SA6HBR/F800_Arduino_ctcss_dtmf/KiCad/F800_arduino_v1.kicad_sch

## KiCad design KiCad/F800_arduino_v1.kicad_sch (2022-08-06)

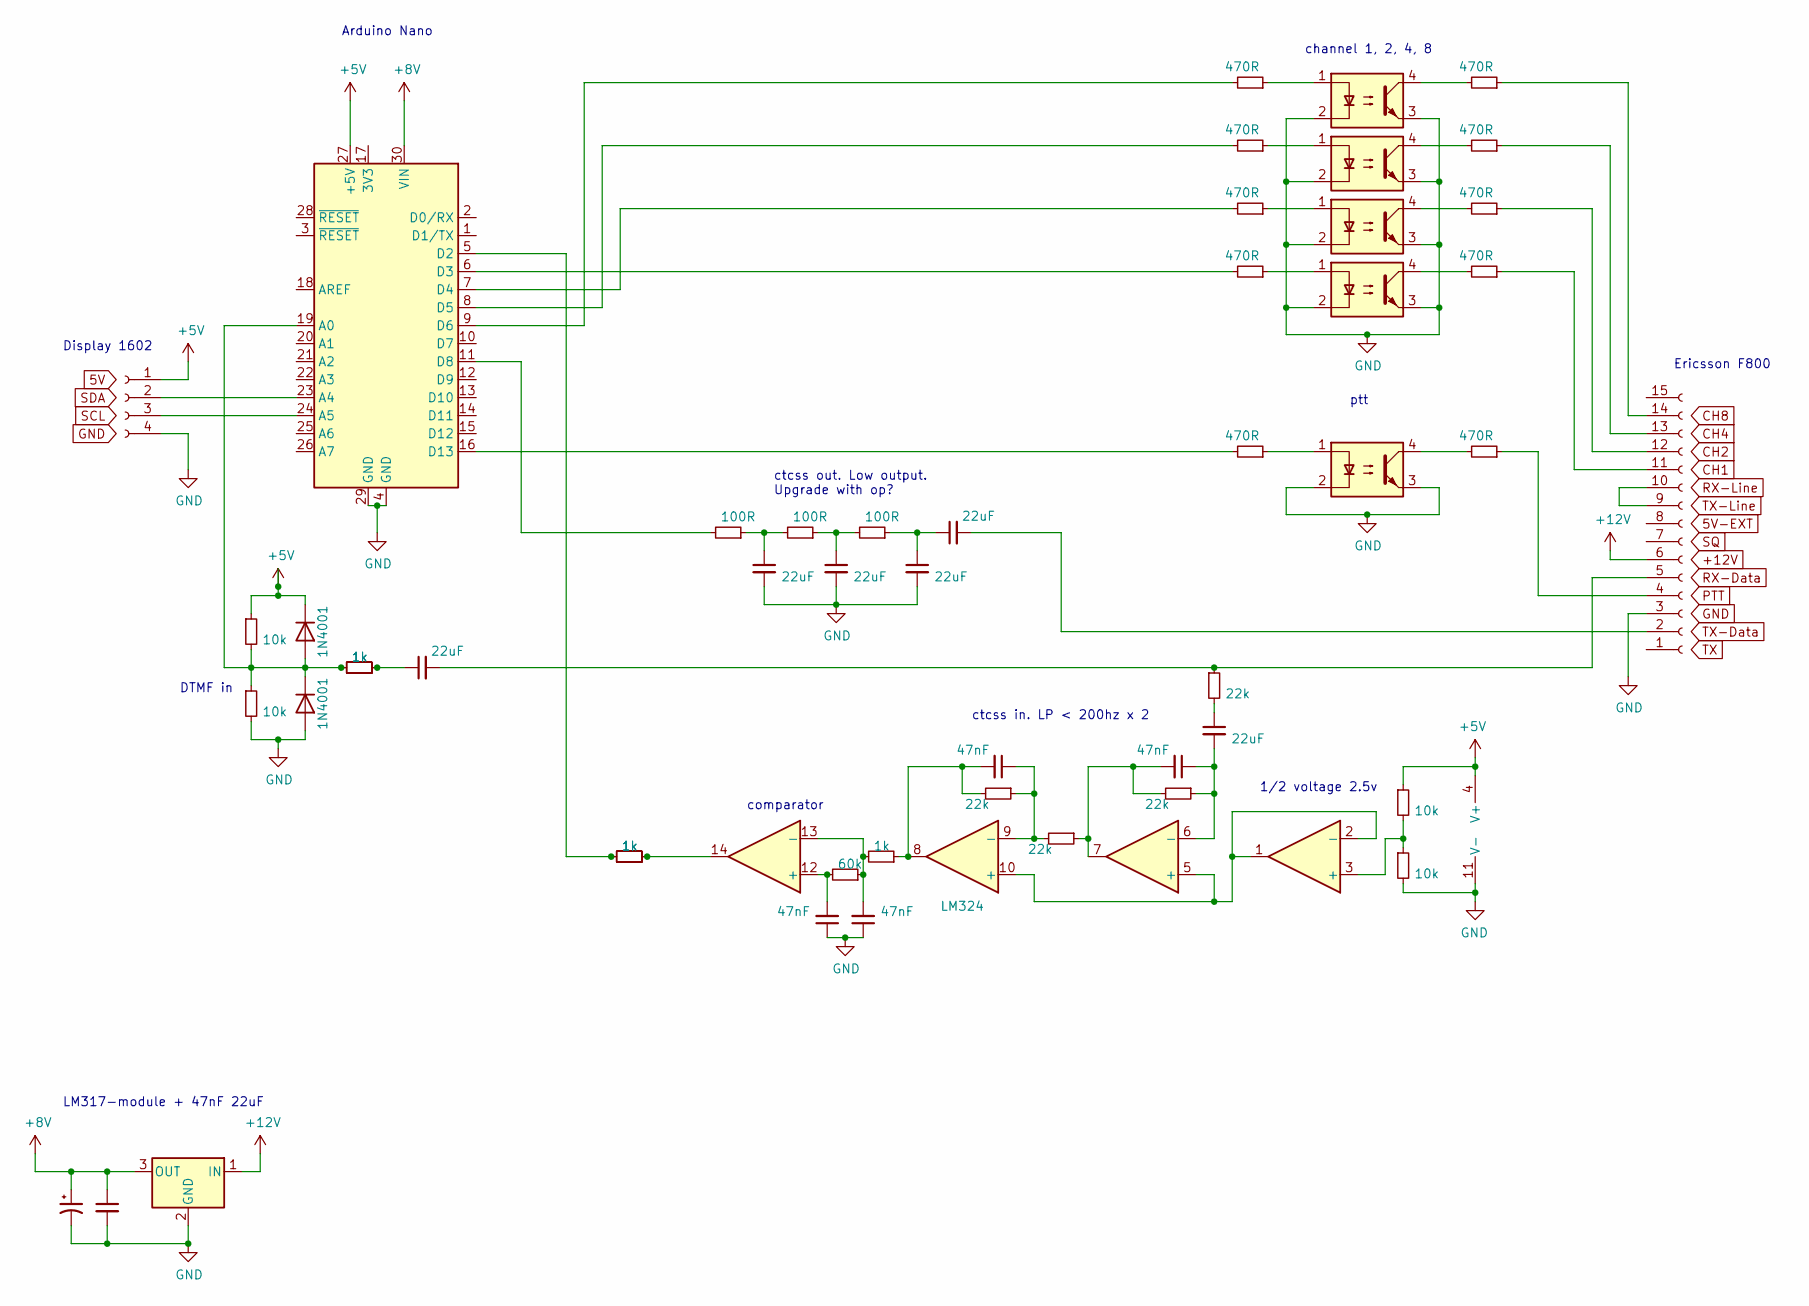
[picture p6: schematic F800_arduino_v1.kicad_sch]

Parts:
.: (no value)
A1: Arduino_Nano_v2.x; Arduino_Nano
C1: C_Small
C2: CP1_Small
Display: Conn_01x04_Female
R1: 470R
U1: PC817; DIP-4_W7.62mm

Connections:
unnamed: ..9, ..10
unnamed: ..14, R1.1
unnamed: A1.23 (A4), Display.2
unnamed: A1.24 (A5), Display.3
unnamed: A1.4 (GND), A1.29 (GND)
unnamed: C1.1, C2.1, U1.3 (OUT)
unnamed: C1.2, C2.2, U1.2 (GND)
unnamed: R1.2, U1.4
unnamed: U1.2 (GND), U1.3 (OUT)

Notes on the sheet:
Display 1602
Arduino Nano
ctcss out. Low output. Upgrade with op?
ptt
DTMF in
1/2 voltage 2.5v
ctcss in. LP < 200hz x 2
Ericsson F800
LM317-module + 47nF 22uF
channel 1, 2, 4, 8
comparator
